RapportTecnologia/kit-de-prototipacao-educacional-e-engenharia/MERCADO.md

# Mercado de microcontroladores, projetos e prototipação (ênfase em educação e IoT)

## 1) Por que microcontroladores e prototipação são estratégicos
Microcontroladores (MCUs) e placas de prototipação são a base prática para transformar conhecimento em **produto físico**: sensores, controle, comunicação, automação, robótica e IoT. Em educação, são um dos meios mais eficientes para ensinar:

- **Programação aplicada** (C/C++, MicroPython, RTOS)
- **Eletrônica e instrumentação** (sensoriamento, condicionamento, ADC/DAC)
- **Sistemas embarcados** (tempo real, consumo energético, confiabilidade)
- **Conectividade** (BLE, Wi‑Fi, LoRa/LPWAN, NB‑IoT, redes industriais)
- **Engenharia de produto** (prototipação rápida, iteração, testes e validação)

Esse conjunto de competências é diretamente reutilizável em projetos de **IoT industrial, agritech, saúde, energia, smart cities e educação tecnológica**.

## 2) Tamanho do mercado: MCUs e IoT (dados públicos e referências)

### 2.1 Mercado global de microcontroladores (MCUs)
- **Tamanho e crescimento**: o mercado global de MCUs é estimado em **US\$ 34,75 bilhões (2025)** e projetado para **US\$ 57,25 bilhões (2030)**, com **CAGR de 10,5%**.
  - Fonte: Mordor Intelligence – *Microcontroller (MCU) Market*.
    - https://www.mordorintelligence.com/industry-reports/microcontroller-mcu-market

- **Indicadores de adoção** (mesma fonte):
  - **Automotivo** liderando por aplicação (31% em 2024).
  - **32-bit** dominando por classe (57% em 2024).
  - **ARM Cortex‑M** com 69% em 2024 e **RISC‑V** crescendo (CAGR 15,4% até 2030).

Esses números ajudam a justificar que MCUs não são “apenas hobby”: são componente central do crescimento de eletrificação, sensores e “edge computing”.

### 2.2 Mercado global de IoT: investimento e crescimento
- **Projeção de mercado (IoT)**: o mercado global de IoT é projetado para crescer de **US$ 547,06 bilhões (2025)** para **US$ 865,20 bilhões (2030)**, com **CAGR de 9,6%**.
  - Fonte: MarketsandMarkets – *Internet of Things (IoT) Market*.
    - https://www.marketsandmarkets.com/Market-Reports/internet-of-things-market-573.html

- **Gastos globais (IoT spending)**: o gasto global com IoT foi estimado em **US$ 805,7 bilhões (2023)** e a IDC projeta que o investimento no ecossistema IoT deve **ultrapassar US$ 1 trilhão em 2026**, com **CAGR de 10,4% (2023–2027)**.
  - Fonte (reportagem citando IDC): RCR Wireless.
    - https://www.rcrwireless.com/20230621/featured/global-iot-spending-exceed-805-billion-this-year-idc

**Leitura prática para este projeto**: IoT cresce de forma sustentada e a maior barreira para adoção/escala costuma ser **talento** (engenharia/tecnologia) + **capacidade de prototipar e testar rapidamente**.

## 3) Brasil: base educacional e potencial de impacto

### 3.1 Educação Superior (tamanho do público-alvo)
- O Brasil alcançou **10 milhões de estudantes no ensino superior em 2024**.
  - Fonte: INEP – *Censo da Educação Superior 2024 (notícia de divulgação)*.
    - https://www.gov.br/inep/pt-br/centrais-de-conteudo/noticias/censo-da-educacao-superior/inep-divulga-resultado-do-censo-superior-2024

Esse universo inclui cursos diretamente relacionados ao uso de kits de prototipação e microcontroladores: **Engenharias, Computação, Automação, Mecatrônica, Física, Tecnologias** e licenciaturas/áreas STEM.

### 3.2 Educação Profissional e Tecnológica (EPT)
- O INEP aponta que a EPT foi a modalidade que mais cresceu na educação básica no período recente: as matrículas passaram de **2,1 milhões (2022)** para **2,4 milhões (2023)**, um aumento de **12,1%**.
  - Fonte: INEP – *Censo Escolar 2023 (notícia)*.
    - https://www.gov.br/inep/pt-br/centrais-de-conteudo/noticias/censo-escolar/matriculas-na-educacao-profissional-aumentaram-12-1

Esse dado é especialmente relevante porque o kit atua exatamente onde a EPT precisa de mais eficácia: **aula prática, laboratório, projetos integradores e formação aplicada**.

### 3.3 Rede Federal e capilaridade (IFs)
- Em 2008, a **Lei nº 11.892** criou **38 Institutos Federais**.
- O MEC informa que, com a expansão, a Rede Federal chegou a **682 unidades**, **mais de 1,5 milhão de matrículas**, e a expansão anunciada prevê **100 novos campi**, levando o total a **782 unidades**.
  - Fonte: MEC – anúncio de 100 novos campi (mar/2024).
    - https://www.gov.br/mec/pt-br/assuntos/noticias/2024/marco/governo-federal-anuncia-100-novos-campi-de-institutos-federais

**Interpretação para este projeto**: a Rede Federal, por si só, já configura uma base nacional extremamente capilarizada para adoção de um kit educacional padronizado, replicável e com foco em projetos.

## 4) Mercado de trabalho e “base produtiva” (técnicos e engenheiros)

- O sistema Confea/Crea encerrou 2023 com **1.121.435 profissionais ativos** (engenharia, agronomia, geociências e tecnólogos, conforme a publicação).
  - Fonte: AEASMS (notícia sobre Confea).
    - https://aeasms.org.br/confea-encerra-2023-com-mais-de-112-milhao-de-profissionais-ativos/

- Pesquisa do Confea (com levantamento amplo) indica **mercado aquecido**: **92% dos profissionais estão em exercício** e **78% atuam na sua área de formação**.
  - Fonte: Confea (notícia) + referência à pesquisa.
    - https://www.confea.org.br/censo-do-confea-92-dos-profissionais-estao-empregados

**Como isso conecta ao kit**:
- Profissionais em atividade demandam **mão de obra que já chegue sabendo prototipar**.
- Instituições de ensino e cursos livres ganham quando a formação inclui **projetos reais** (sensores, comunicação, controle, telemetria, automação, coleta de dados).

## 5) Startups e ecossistema: evidência de demanda por embedded/IoT
O Brasil tem um ecossistema ativo de soluções com **tecnologia embarcada** e conectividade. Como evidência (lista não-exaustiva), a Liga Ventures publicou um mapeamento com **48 startups de IoT**.

- Fonte: Liga Ventures – *48 startups de IoT (Internet das Coisas)*.
  - https://liga.ventures/insights/startups/48-startups-de-iot-internet-das-coisas/

Exemplos presentes na lista:
- **Agrosmart** (AgTech/IoT)
- **Konker Labs** (plataforma/soluções IoT)
- **Oxiot**
- **SolfInftec**
- **Strider**
- **Nexxto**

Esses casos reforçam que há mercado (clientes e empresas) para:
- Sensores e telemetria
- Monitoramento/controle remoto
- Gestão de ativos
- Sistemas de automação
- Conectividade e análise de dados

## 6) Prototipação: por que gera valor (do laboratório ao produto)
Um kit educacional de microcontroladores bem desenhado reduz custo e tempo em:

- **Curva de aprendizagem**: menos tempo “brigando com setup”, mais tempo fazendo projeto.
- **Iteração**: protótipos rápidos permitem testar hipóteses e corrigir cedo.
- **Padronização didática**: facilita replicar cursos e laboratórios (IFs, escolas técnicas, universidades).
- **Empregabilidade**: habilidades práticas alinhadas ao que IoT/embedded exigem.

## 7) Conclusão: mercado latente e crescimento (IoT como motor)
Os indicadores de mercado (MCUs e IoT) e os números de educação no Brasil sustentam a tese de um **mercado latente com forte crescimento**, especialmente puxado por **IoT**, eletrificação e digitalização de processos.

- Há **demanda tecnológica** (mercado global em expansão).
- Há **base educacional enorme** (10 milhões no superior; 2,4 milhões na EPT).
- Há **capilaridade institucional** (Rede Federal com centenas de unidades e mais de 1,5 milhão de matrículas).
- Há **ecossistema empresarial** (startups e indústria buscando soluções embarcadas).

Isso justifica o investimento em um kit educacional/prototipação que acelere formação e projetos em escala.
