RapportTecnologia/kit-de-prototipacao-educacional-e-engenharia/docs/firmware.md

---
layout: page
title: "Firmware"
subtitle: "Código e projetos de firmware do KEPR"
permalink: /firmware/
is_category: true
---

O firmware principal está na pasta `firmware_UCE/` no repositório.
