RapportTecnologia/kit-de-prototipacao-educacional-e-engenharia/docs/sobre.md

---
layout: page
title: "Sobre"
subtitle: "Sobre o projeto e o autor"
permalink: /sobre/
---

## O projeto

O **KEPR (Kit Educacional e Prototipação Rapport)** é um ecossistema de hardware para prototipação e aprendizagem em sistemas embarcados e IoT, com foco em modularidade e expansão.

Objetivos principais:

- reduzir atrito no desenvolvimento e nos estudos;
- padronizar conexão/expansão via barramento (UCE);
- facilitar testes, validações e iterações;
- suportar diferentes famílias de microcontroladores.

## O autor

Projeto iniciado com fins **educacionais** e de evolução técnica de **Carlos Delfino**.

## Links úteis

- Repositório: [github.com/RapportTecnologia/kit-de-prototipacao-educacional-e-engenharia](https://github.com/RapportTecnologia/kit-de-prototipacao-educacional-e-engenharia)
- Site: [rapport.tec.br](https://rapport.tec.br)
