RapportTecnologia/kit-de-prototipacao-educacional-e-engenharia/docs/_posts/2026-01-01-bem-vindo-ao-kepr.md

---
layout: post
title: "Bem-vindo ao KEPR"
date: 2026-01-01 00:00:00 -0300
tags: [KEPR]
---

Este é o primeiro post do site do **KEPR**.

Aqui você vai encontrar atualizações, decisões de arquitetura do barramento (UCE), evolução dos módulos e materiais de estudo relacionados ao kit.
