RapportTecnologia/kit-de-prototipacao-educacional-e-engenharia/docs/_posts/2026-01-01-documentacao-inicial.md

---
layout: post
title: "Documentação inicial do projeto"
date: 2026-01-01 00:10:00 -0300
tags: [KEPR]
---

Referências rápidas presentes no repositório:

- [`UCE_BOARD.md`](https://github.com/RapportTecnologia/kit-de-prototipacao-educacional-e-engenharia/blob/main/UCE_BOARD.md)
- [`CHANGELOG.md`](https://github.com/RapportTecnologia/kit-de-prototipacao-educacional-e-engenharia/blob/main/CHANGELOG.md)
- [`NETWORK_MOD.md`](https://github.com/RapportTecnologia/kit-de-prototipacao-educacional-e-engenharia/blob/main/NETWORK_MOD.md)
- [`WERELESS_MOD.md`](https://github.com/RapportTecnologia/kit-de-prototipacao-educacional-e-engenharia/blob/main/WERELESS_MOD.md)
- [`DEBUG_MOD.md`](https://github.com/RapportTecnologia/kit-de-prototipacao-educacional-e-engenharia/blob/main/DEBUG_MOD.md)

À medida que o projeto evoluir, esta lista pode ser atualizada com novas seções e guias.
