RapportTecnologia/kit-de-prototipacao-educacional-e-engenharia/datasheets/MosFETs/BSS138 - N-Channel Logic Level Enhancement Mode Field Effect Transistor - onsemi.jpg

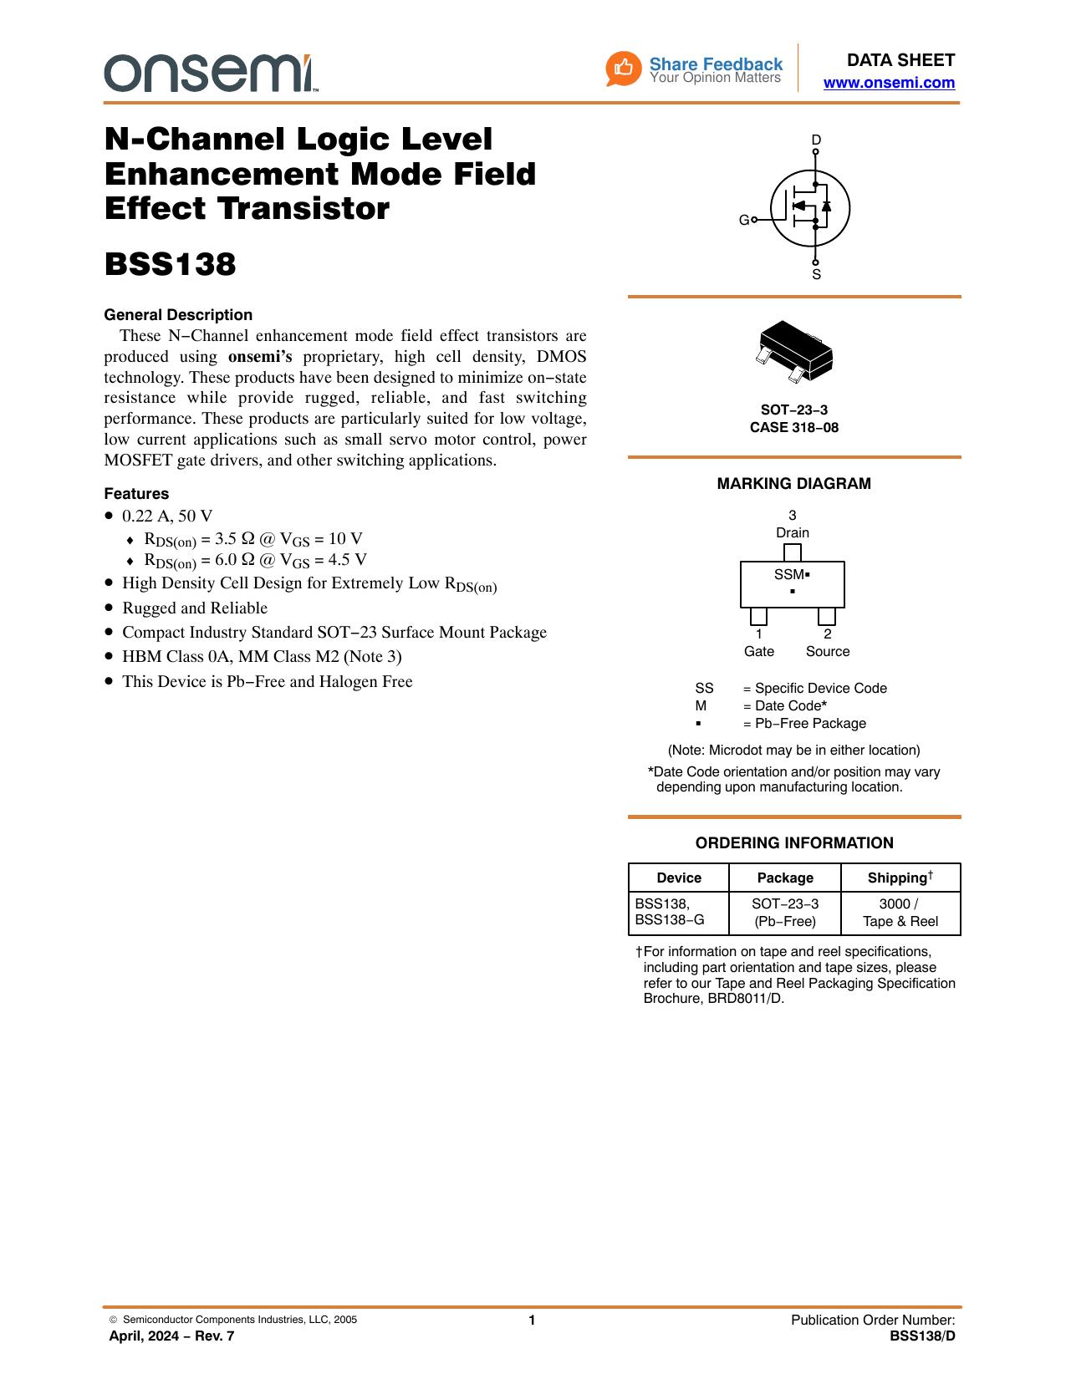
datasheets/MosFETs/BSS138 - N-Channel Logic Level Enhancement Mode Field Effect Transistor - onsemi.jpg
