RapportTecnologia/kit-de-prototipacao-educacional-e-engenharia/docs/assets/img/kepr-pcb-bottom-3d.png

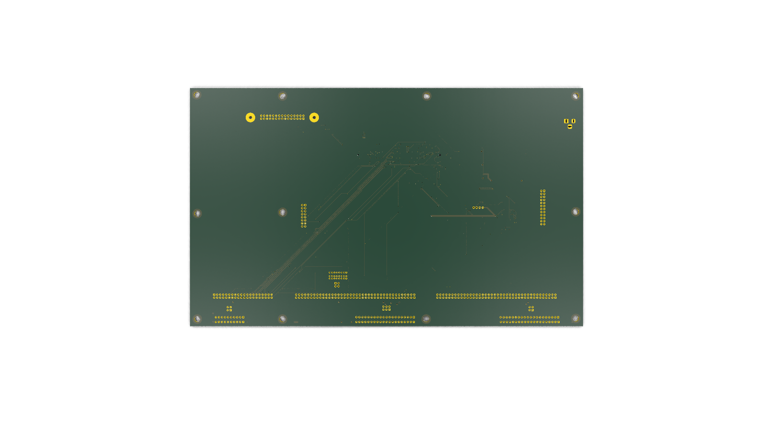
docs/assets/img/kepr-pcb-bottom-3d.png
