RapportTecnologia/kit-de-prototipacao-educacional-e-engenharia/docs/assets/img/pcbs/mcu-board-stm32n6/bottom-3d.png

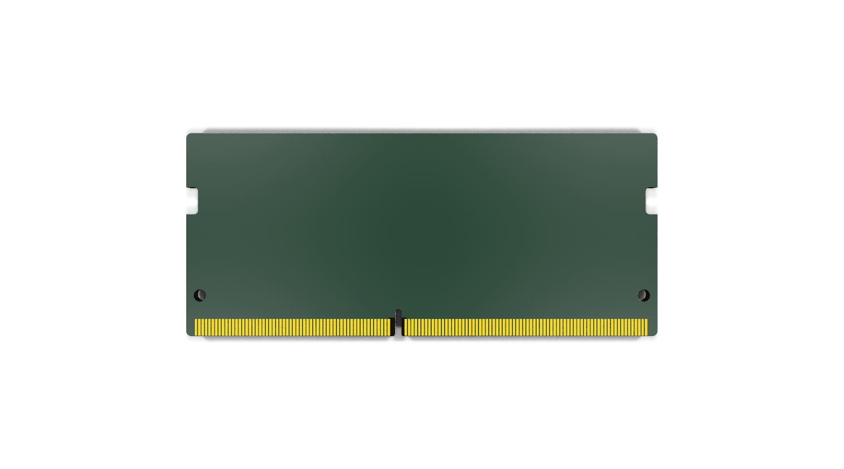
docs/assets/img/pcbs/mcu-board-stm32n6/bottom-3d.png
