RapportTecnologia/kit-de-prototipacao-educacional-e-engenharia/datasheets/System-Level ESD Protection Guide (Rev. E) - Texas Instruments, Incorporated [SSZB130,E.jpg

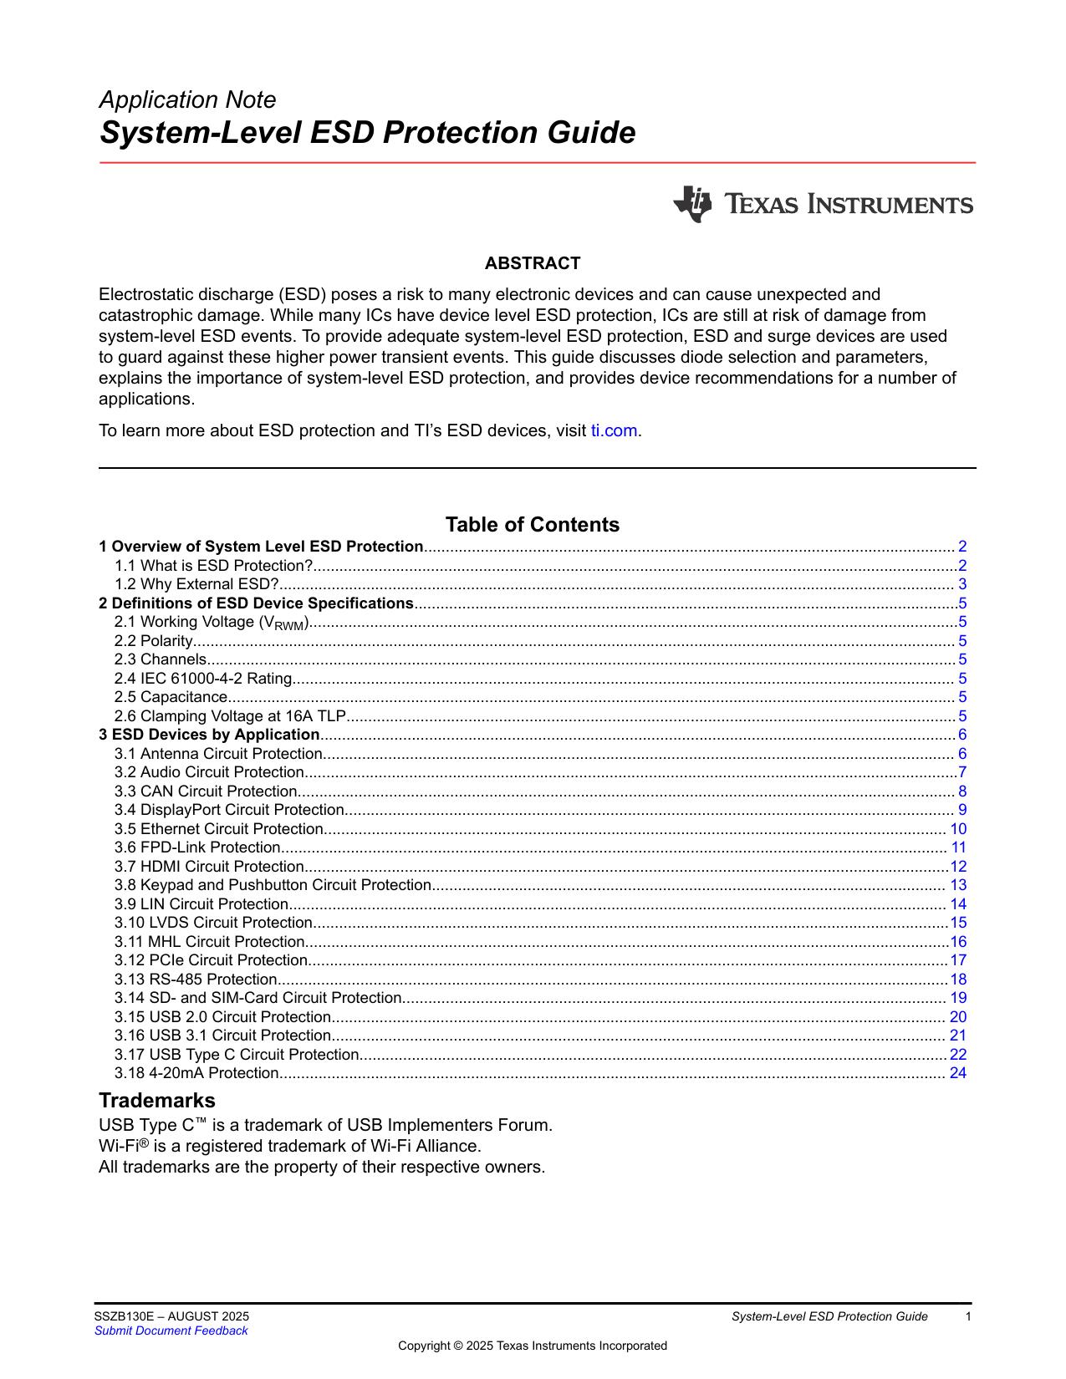
datasheets/System-Level ESD Protection Guide (Rev. E) - Texas Instruments, Incorporated [SSZB130,E.jpg
